jenatton-Malik/zvs-driver/simulations/ZVS_spice.asc

C1: cap; 0.33µF; V=1200 Irms=9 Rser=0.007
C2: cap; 0.33µF; V=1200 Irms=9 Rser=0.007
D1: zener; BZX84C12L
D2: zener; BZX84C12L
D3: diode; UF4007
D4: diode; UF4007
L3: ind; 50µ; Rser=1m
L5: ind; 100µ; Rser=1m
M5: nmos; IRFP260N
M6: nmos; IRFP260N
R1: res; 470; pwr=2
R2: res; 471; pwr=2
R3: res; 10K; pwr=0.25
R4: res; 10K; pwr=0.25
V1: voltage; 12
Named nets: 0
.tran 0 0.5 0 1 uic
.model UF4007 D(Is=12.2n Rs=42.6m N=1.63 Cjo=12.1p M=0.333 Vj=0.75 Fc=0.5 Bv=1000 Ibv=10u Tt=75n)
.model IRFP260N NMOS(Level=3 Gamma=0 Vto=4.0 Phi=0.6 Is=1e-14 Js=0 Pb=0.8 Fc=0.5 Cgso=3.15e-09 Cgdo=4.67e-10 Rg=1.35 Rd=0.012 R_s=0.005 Rb=0.0122 Lambda=0 Tox=0 Tref=27 W=1 L=100u Rs=0.005 Kp=22.8u)
